stefaweb/Q17-Amplifier/Q17-Mini-3.0/Q17-Mini-L1-measure.jpg

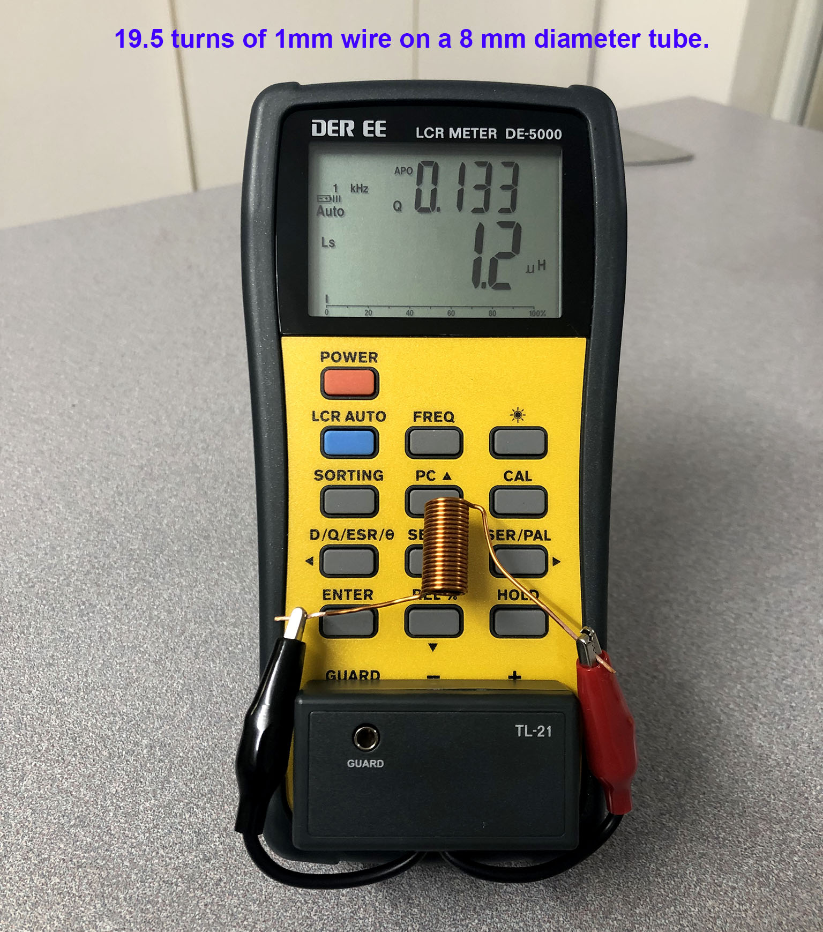
Q17-Mini-3.0/Q17-Mini-L1-measure.jpg
