stefaweb/Q17-Amplifier/Q17-Mini-PCB-1.0.8 2.jpg

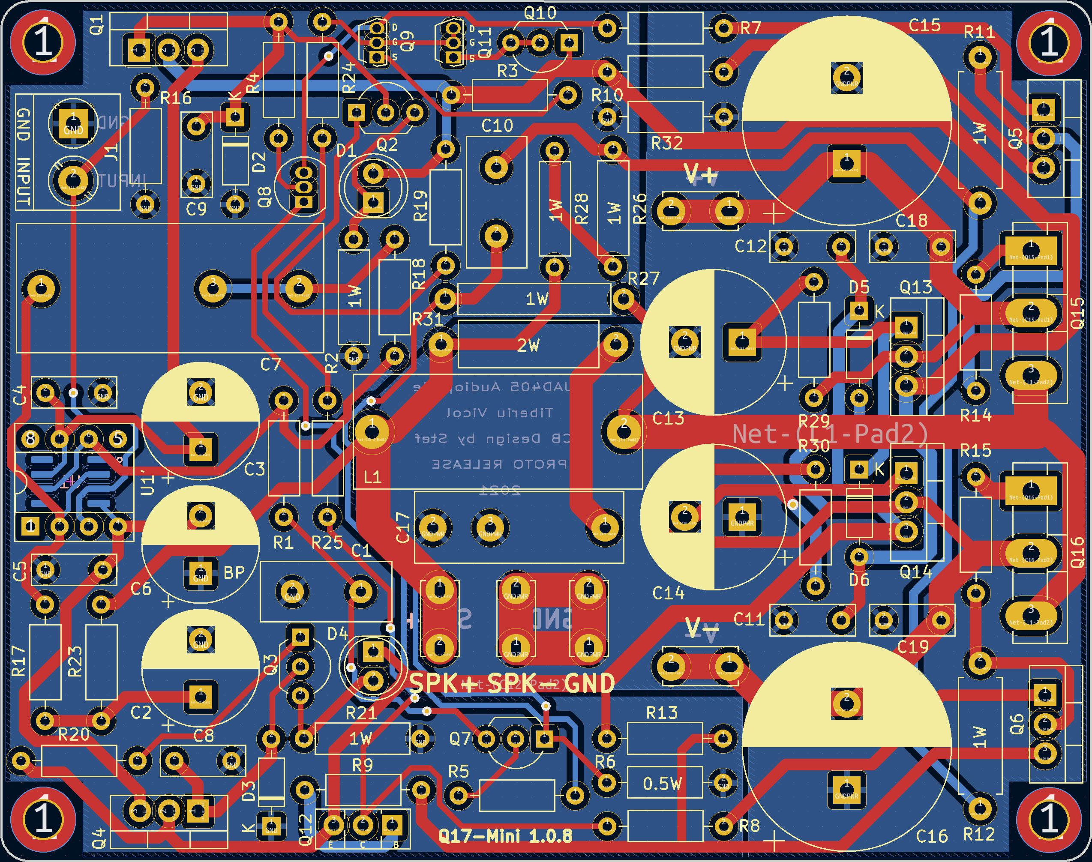
Q17-Mini-PCB-1.0.8 2.jpg
