stefaweb/Q17-Amplifier/NDC7003P KiCad/NDC7003P-Symbol.png

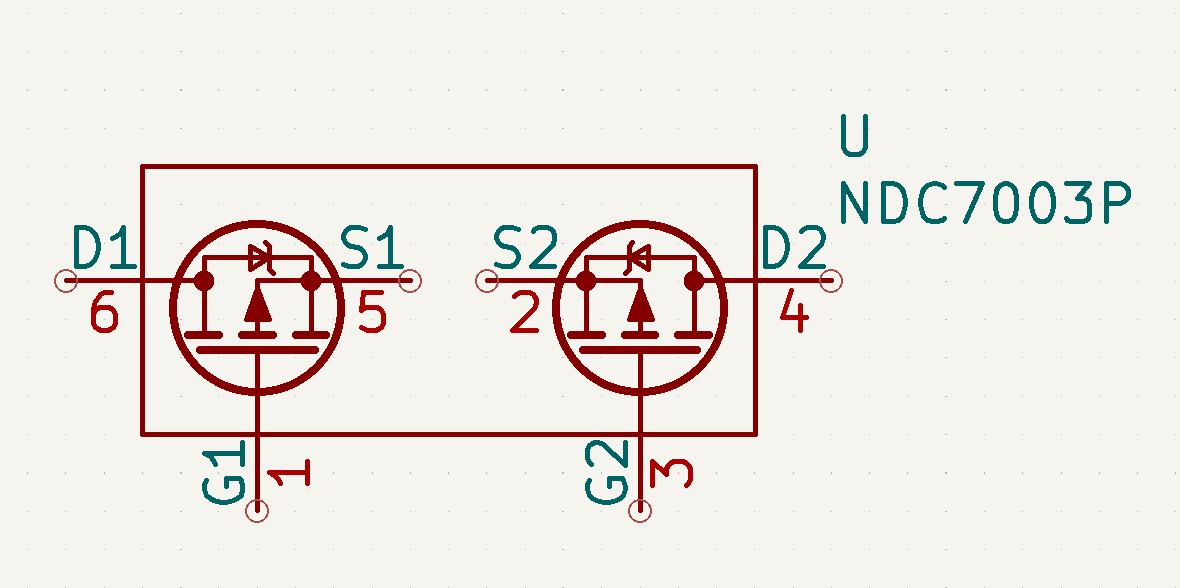
NDC7003P KiCad/NDC7003P-Symbol.png
