stefaweb/Q17-Amplifier/Q17-Mini-1.1.1/Q17-Mini-PCB.jpg

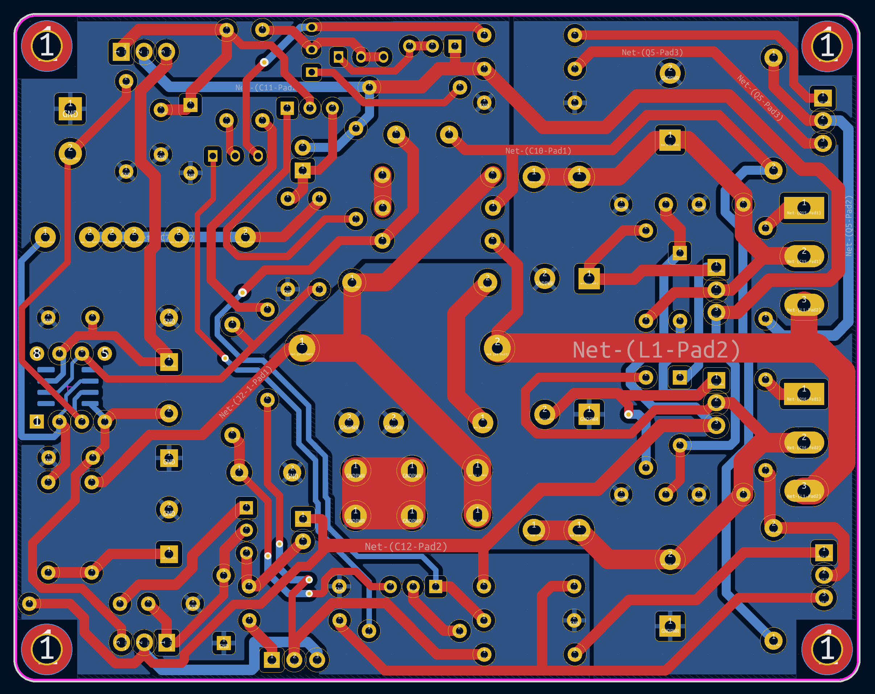
Q17-Mini-1.1.1/Q17-Mini-PCB.jpg
