stefaweb/Q17-Amplifier/Q17-Mini-3.0/Drilling diagram Q17-Mini v3.jpg

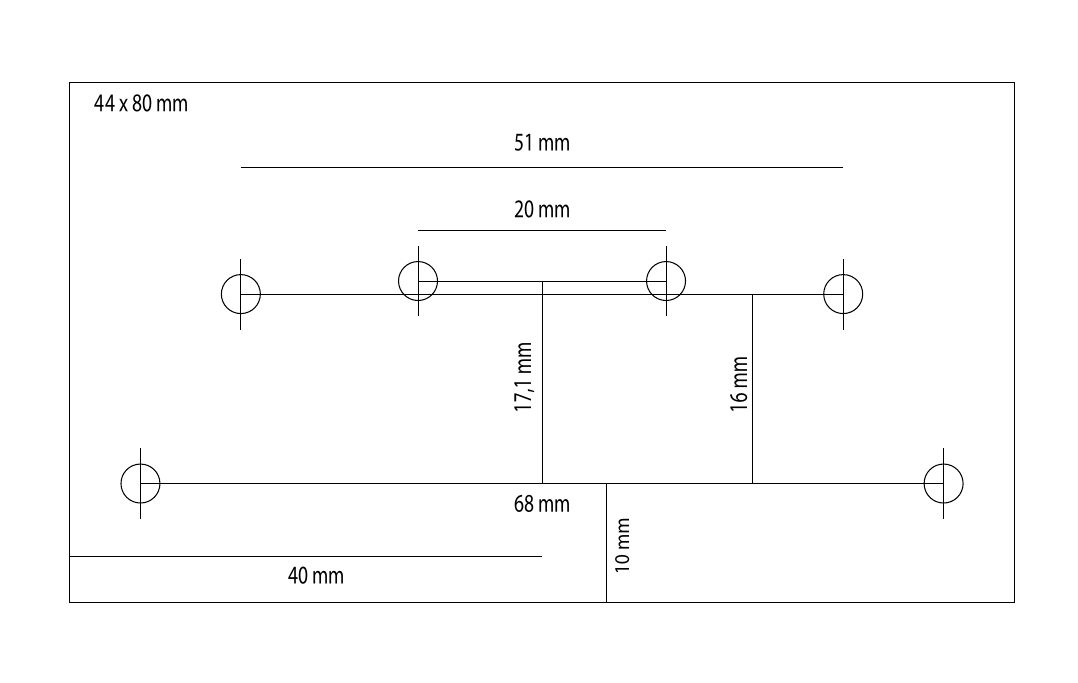
Q17-Mini-3.0/Drilling diagram Q17-Mini v3.jpg
