stefaweb/Q17-Amplifier/Q17-Mini-3.0/Measures Q17-Mini 3.0/Q17-Mini-3.0-spectrum_OPA828.jpg

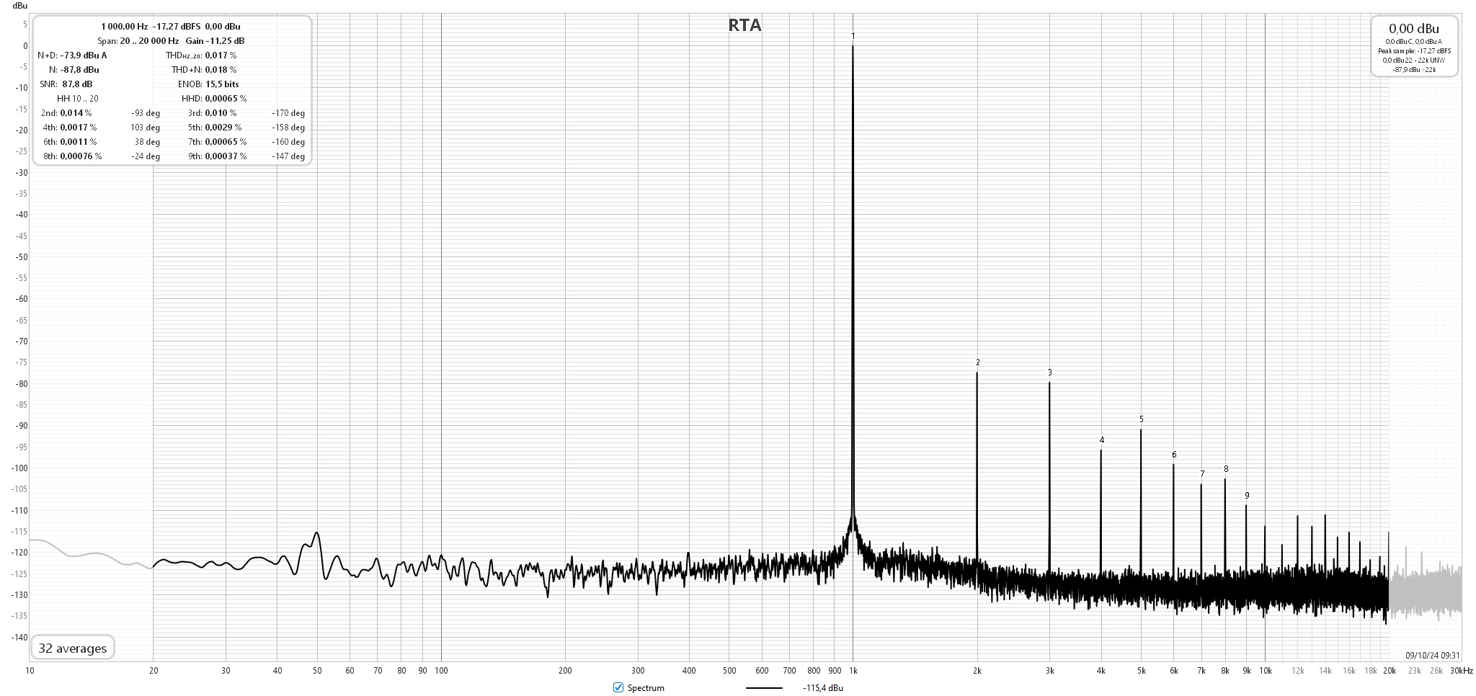
Q17-Mini-3.0/Measures Q17-Mini 3.0/Q17-Mini-3.0-spectrum_OPA828.jpg
