stefaweb/Q17-Amplifier/Q17-Mini-3.0/Q17-Mini-PCB-FRONT.jpg

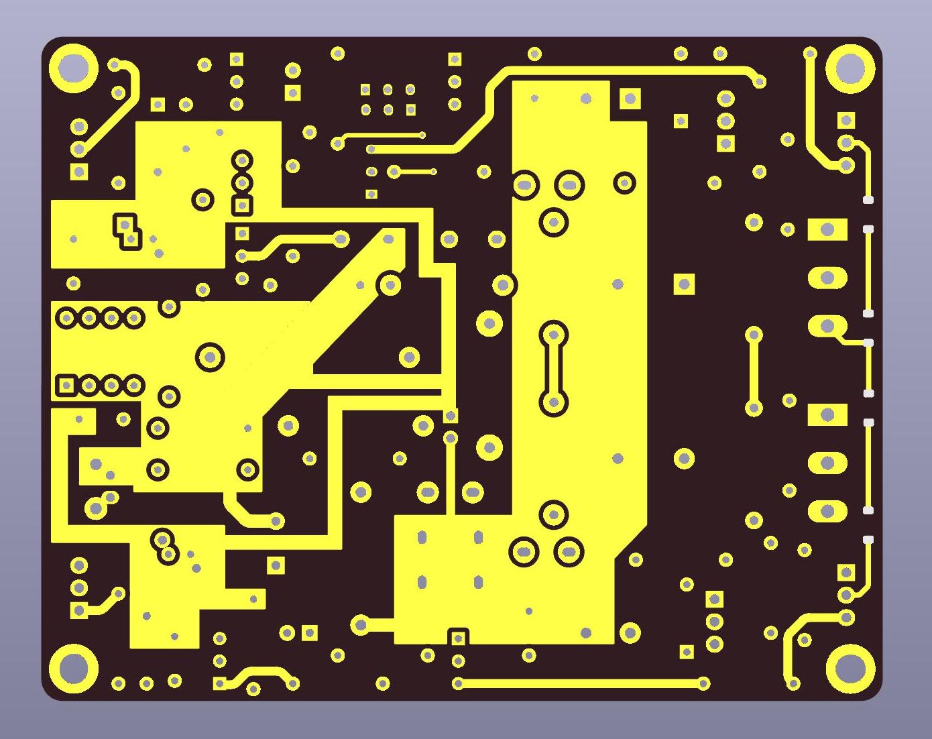
Q17-Mini-3.0/Q17-Mini-PCB-FRONT.jpg
