stefaweb/Q17-Amplifier/Q17-PCB-Coil 1.1/pcb_coil_1.2uH.jpg

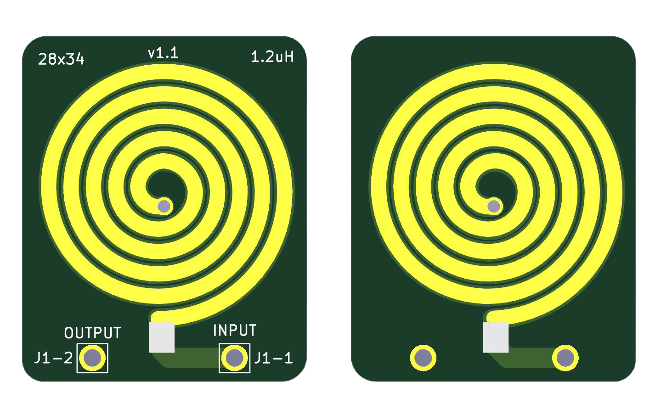
Q17-PCB-Coil 1.1/pcb_coil_1.2uH.jpg
