stefaweb/Q17-Amplifier/Q17-TURBO 1.0/Q17-TURBO-3D.jpg

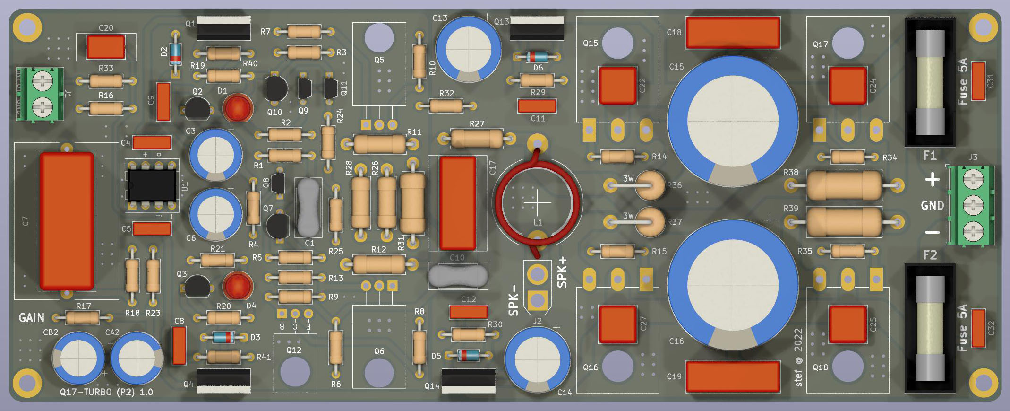
Q17-TURBO 1.0/Q17-TURBO-3D.jpg
