stefaweb/Q17-Amplifier/Q17-TURBO 1.0/Q17-TURBO-COIL-1.2uH/Wire_1.5mm2.jpeg

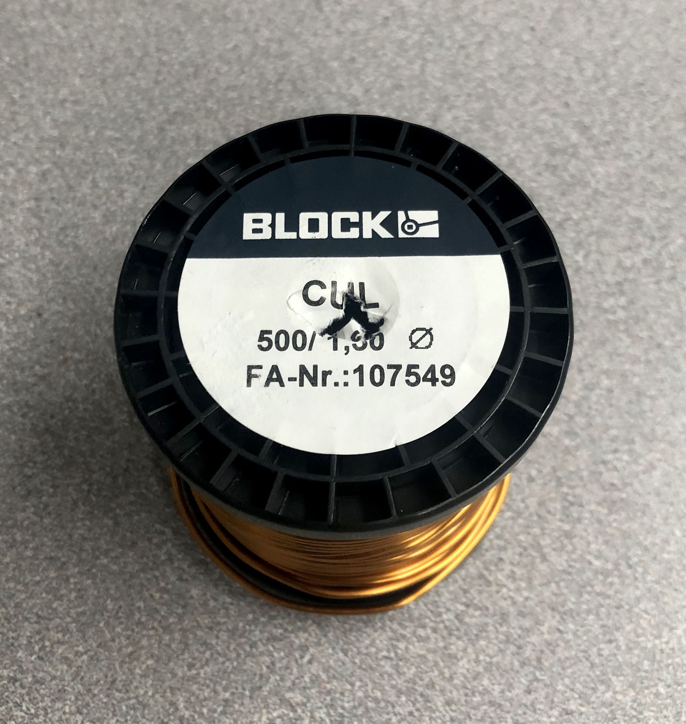
Q17-TURBO 1.0/Q17-TURBO-COIL-1.2uH/Wire_1.5mm2.jpeg
