stefaweb/Q17-Amplifier/Q17-TURBO-2.0/Mounting Plate-Q17-Turbo-216x80-1.0.png

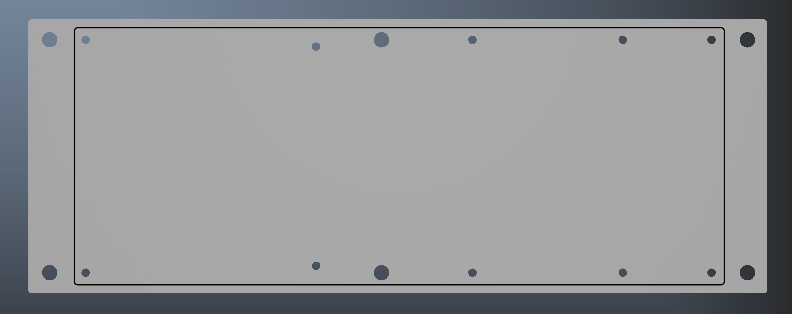
Q17-TURBO-2.0/Mounting Plate-Q17-Turbo-216x80-1.0.png
