stefaweb/Q17-Amplifier/Q17-TURBO-2.0/Q17-Turbo v2 Damping Factor.jpg

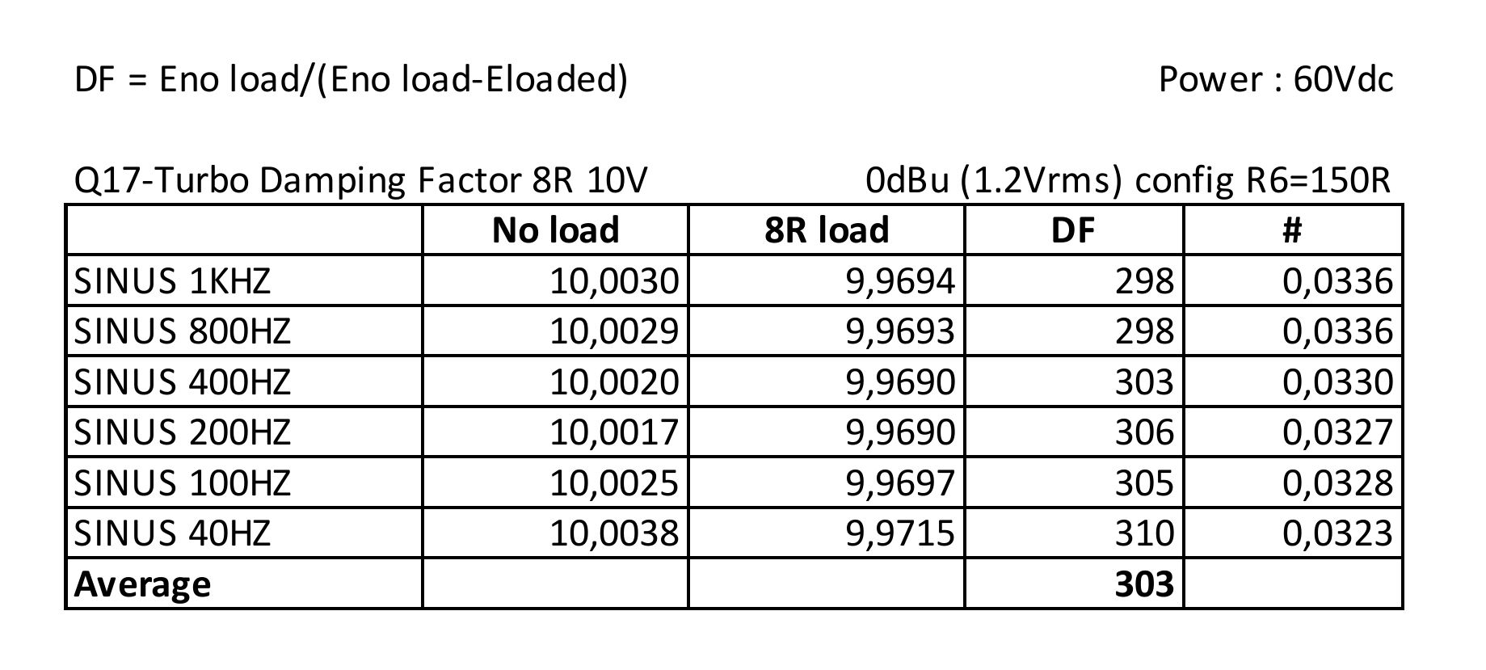
Q17-TURBO-2.0/Q17-Turbo v2 Damping Factor.jpg
