stefaweb/Q17-Amplifier/Q17-TURBO-2.0/Q17-TURBO-3D-BACK.jpg

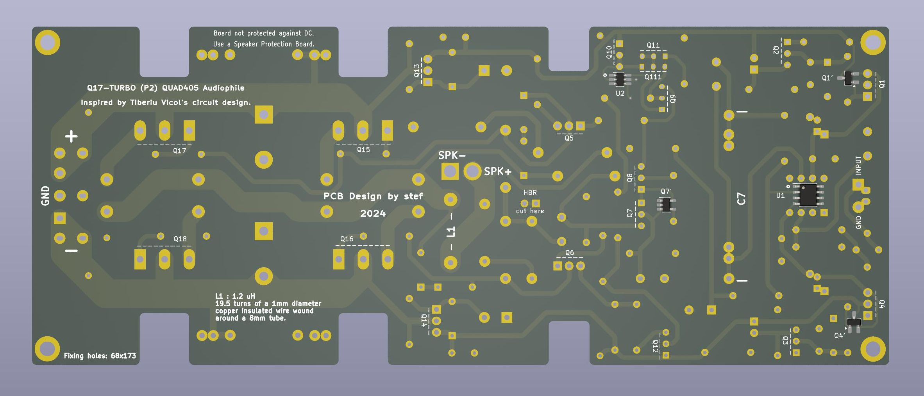
Q17-TURBO-2.0/Q17-TURBO-3D-BACK.jpg
