stefaweb/Q17-Amplifier/Q17-TURBO-2.0/Q17-TURBO-3D-VIEW.jpg

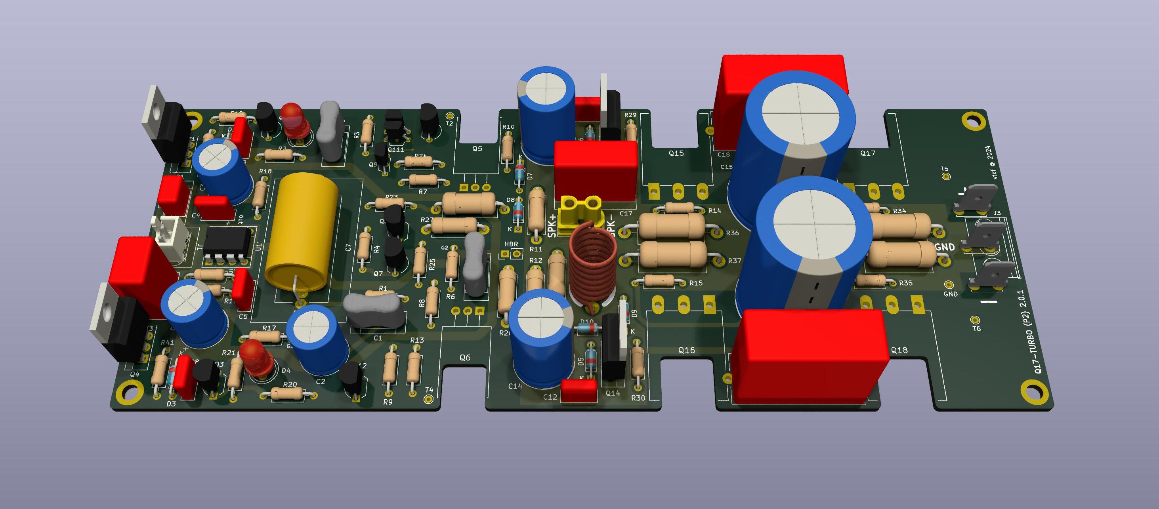
Q17-TURBO-2.0/Q17-TURBO-3D-VIEW.jpg
