stefaweb/Q17-Amplifier/Q17-Mini-3.0/Measures Q17-Mini 3.0/Q17-Mini-3.0_distorsion_1W_configA4.jpg

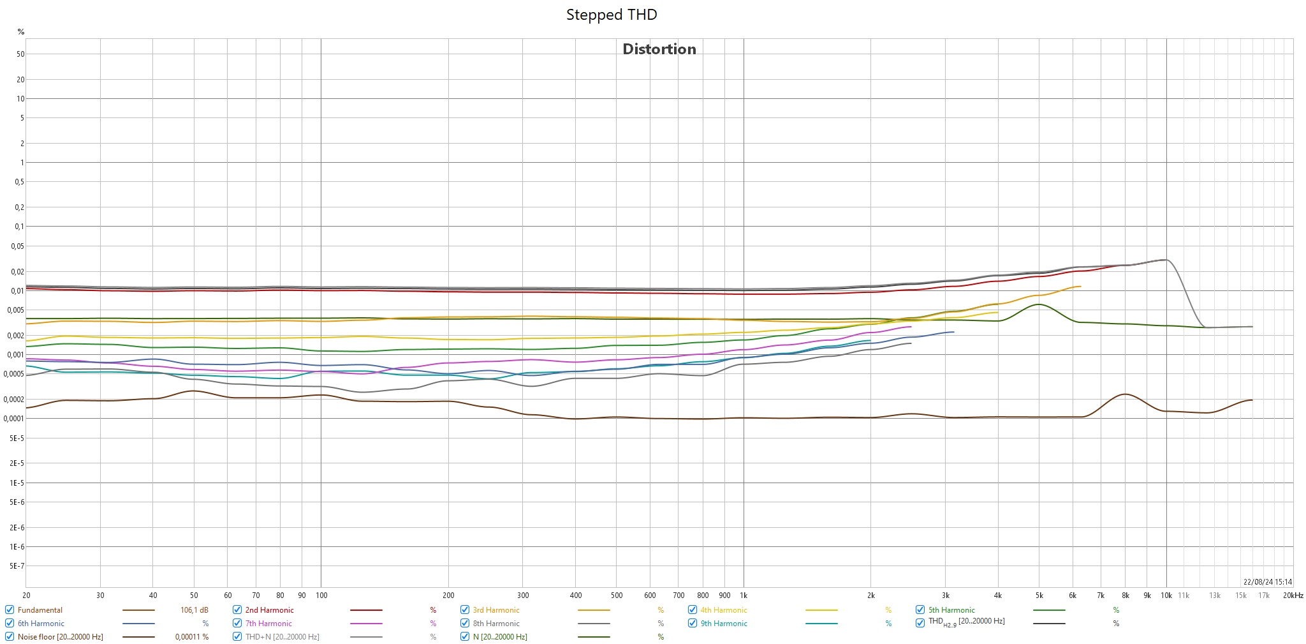
Q17-Mini-3.0/Measures Q17-Mini 3.0/Q17-Mini-3.0_distorsion_1W_configA4.jpg
