stefaweb/Q17-Amplifier/Q17-Mini-3.0/Measures Q17-Mini 3.0/SQUARE_1KHz_1W.jpg

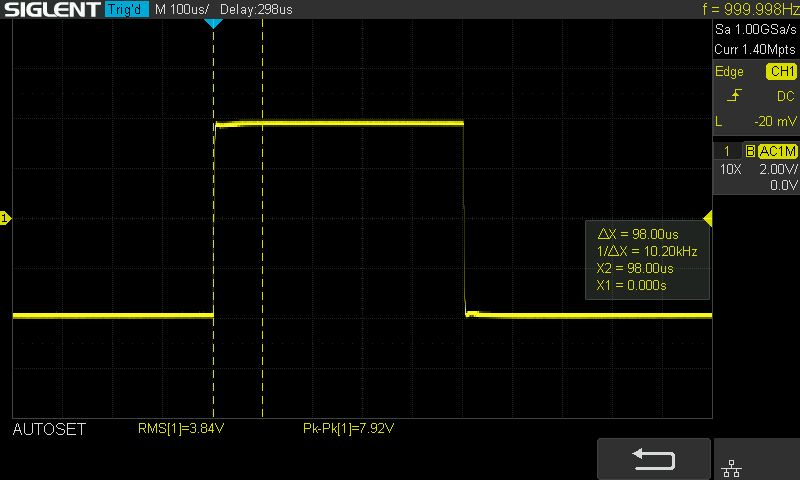
Q17-Mini-3.0/Measures Q17-Mini 3.0/SQUARE_1KHz_1W.jpg
