stefaweb/Q17-Amplifier/Q17-TURBO 1.0/Measures Q17-Turbo 1.0/Q17-Turbo-square-1Khz-50v-clip.jpg

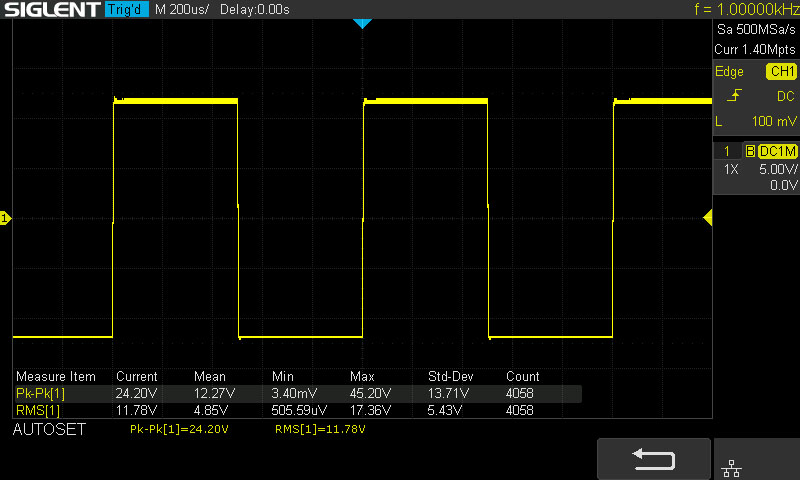
Q17-TURBO 1.0/Measures Q17-Turbo 1.0/Q17-Turbo-square-1Khz-50v-clip.jpg
