stefaweb/Q17-Amplifier/Q17-TURBO-2.0/Measures Q17-Turbo 2.0/SINUS_1KHz_1W.jpg

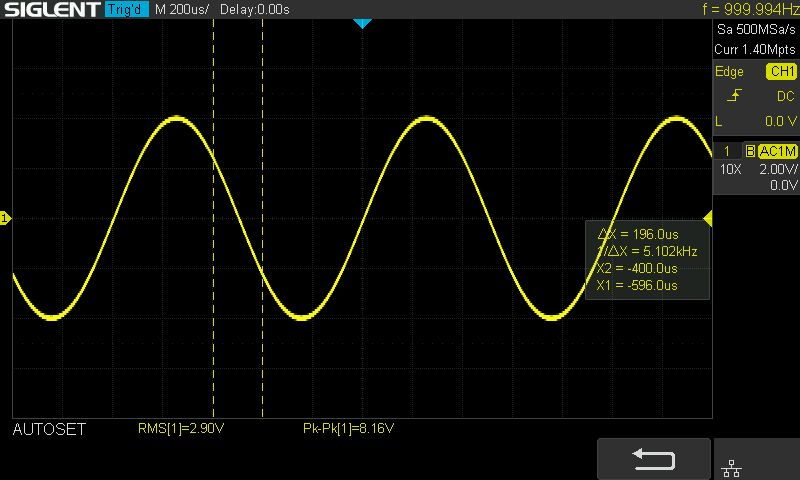
Q17-TURBO-2.0/Measures Q17-Turbo 2.0/SINUS_1KHz_1W.jpg
