stefaweb/Q17-Amplifier/KiCad source/Q17-95x75.kicad_sch

## KiCad design KiCad source/Q17-95x75.kicad_sch (2021-11-15)

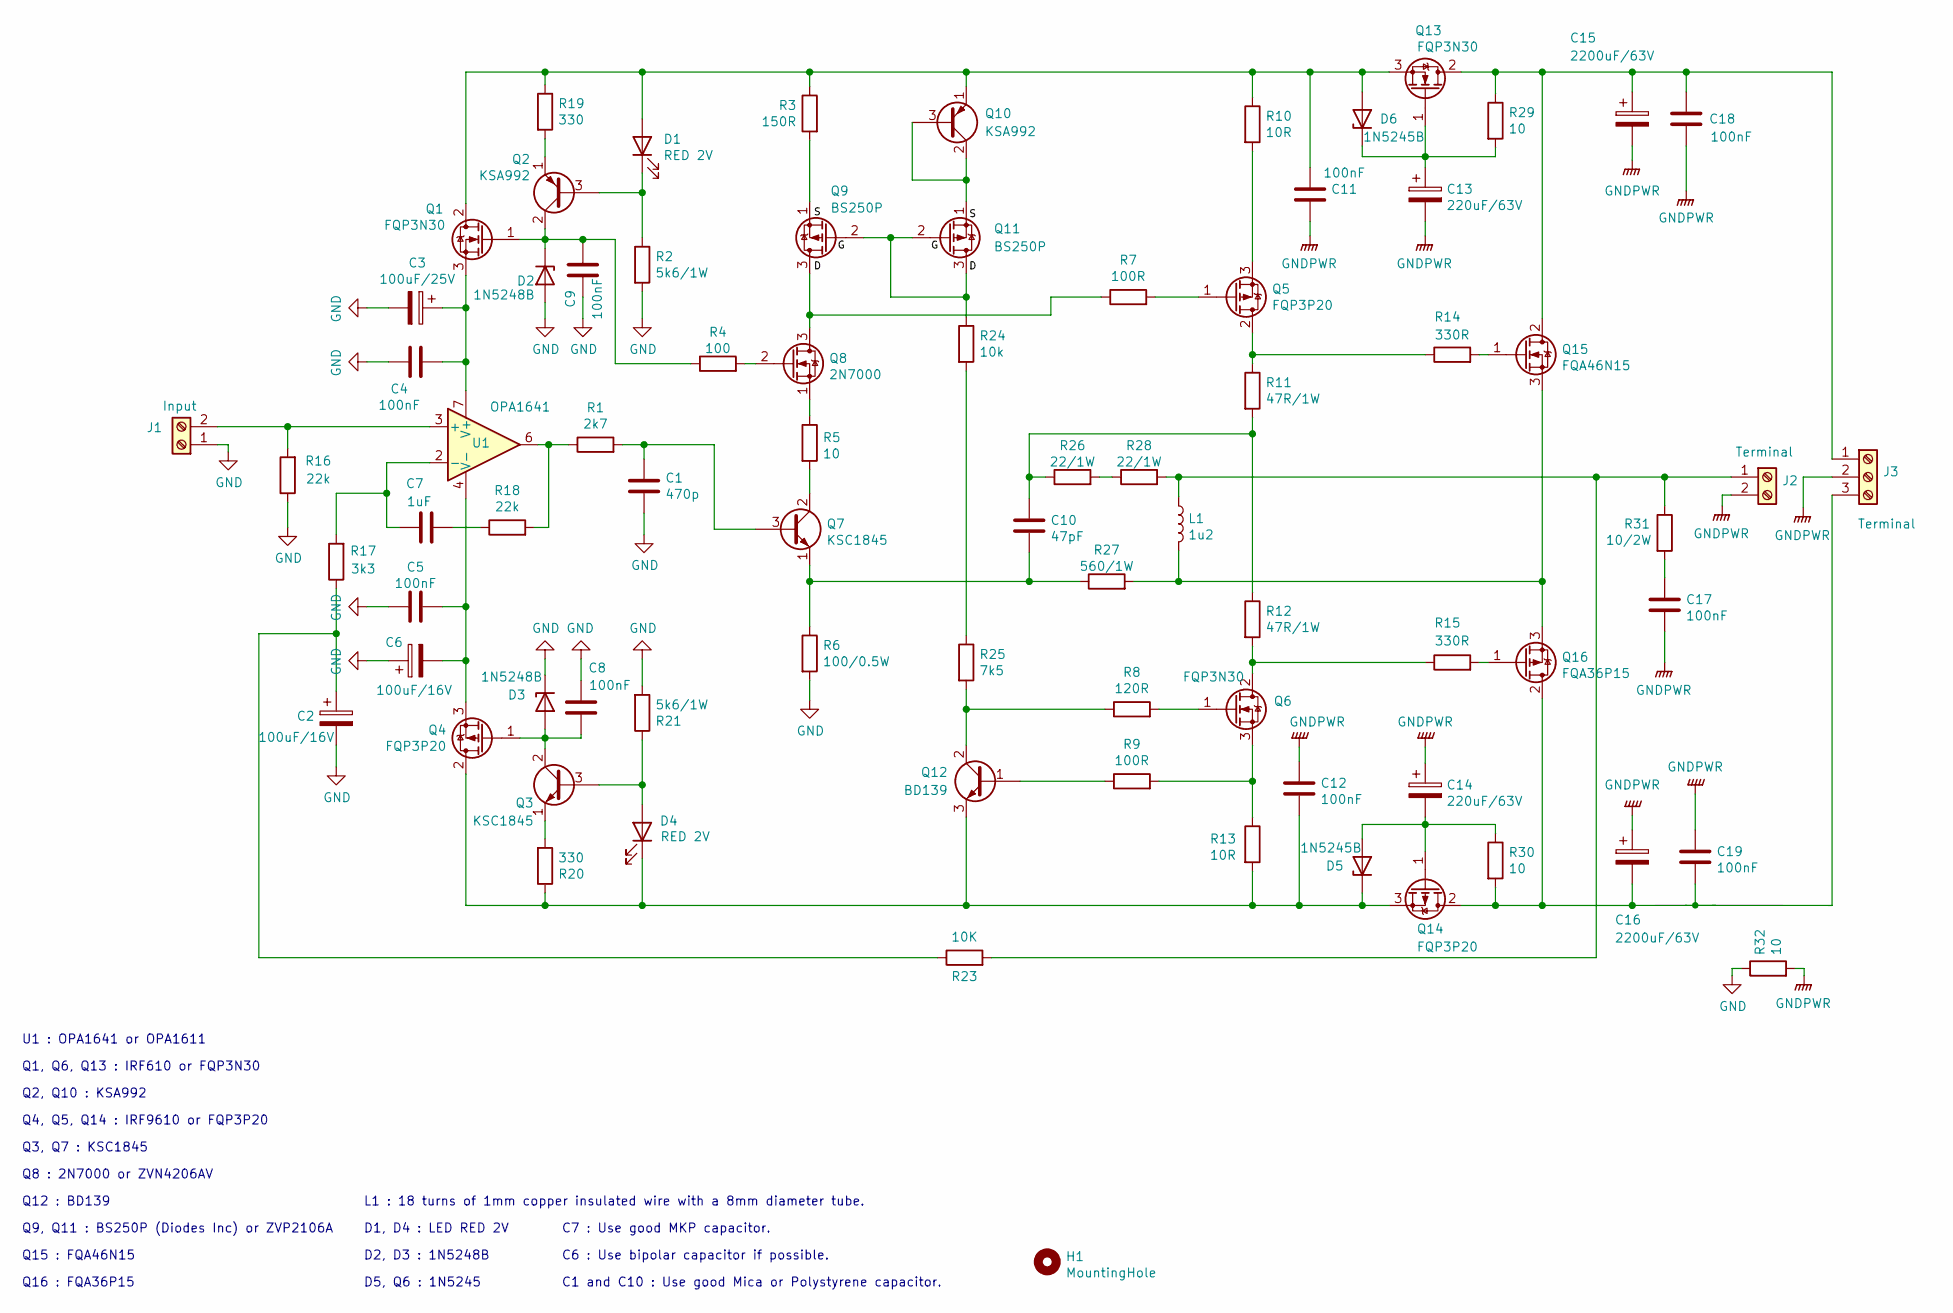
[picture p69: schematic Q17-95x75.kicad_sch]

Parts:
C1: 470p; C_Disc_D11.0mm_W5.0mm_P7.50mm
C2, C6: 100uF/16V; C_Radial_D10.0mm_H12.5mm_P5.00mm
C3: 100uF/25V; C_Radial_D10.0mm_H12.5mm_P5.00mm
C4, C5, C8, C9, C11, C12, C18, C19: 100nF; C_Disc_D7.5mm_W2.5mm_P5.00mm
C7: 1uF; CP_Axial_L26.5mm_D20.0mm_P33.00mm_Horizontal
C10: 47pF; C_Disc_D11.0mm_W5.0mm_P7.50mm
C13, C14: 220uF/63V; CP_Radial_D10.0mm_P5.00mm_P7.50mm
C15, C16: 2200uF/63V; CP_Radial_D18.0mm_P7.50mm
C17: 100nF; C_Rect_L18.0mm_W11.0mm_P15.00mm_FKS3_FKP3
D1, D4: RED 2V; LED_D5.0mm_Clear
D2, D3: 1N5248B; D_DO-35_SOD27_P7.62mm_Horizontal
D5, D6: 1N5245B; D_DO-35_SOD27_P7.62mm_Horizontal
H1: MountingHole; MountingHole_3.2mm_M3_Pad_Via
J1: Input; Stocko_MKS_1651-6-0-202_1x2_P2.50mm_Vertical
J2: Terminal; AMASS_XT30U-F_1x02_P5.0mm_Vertical
J3: Terminal; TerminalBlock_Altech_AK300-3_P5.00mm
L1: 1u2; L
Q1, Q6, Q13: FQP3N30; TO-220-3_Vertical
Q2, Q10: KSA992; TO-92
Q3, Q7: KSC1845; TO-92
Q4, Q5, Q14: FQP3P20; TO-220-3_Vertical
Q8: 2N7000; TO-92_Inline
Q9, Q11: BS250P; TO-92_Inline
Q12: BD139; TO-126-3_Vertical
Q15: FQA46N15; TO-3P-3_Horizontal_TabDown
Q16: FQA36P15; TO-3P-3_Horizontal_TabDown
R1: 2k7; R_Axial_DIN0207_L6.3mm_D2.5mm_P10.16mm_Horizontal
R2, R21: 5k6/1W; R_Axial_DIN0207_L6.3mm_D2.5mm_P10.16mm_Horizontal
R3: 150R; R_Axial_DIN0207_L6.3mm_D2.5mm_P10.16mm_Horizontal
R4: 100; R_Axial_DIN0207_L6.3mm_D2.5mm_P10.16mm_Horizontal
R5, R29, R30, R32: 10; R_Axial_DIN0207_L6.3mm_D2.5mm_P10.16mm_Horizontal
R6: 100/0.5W; R_Axial_DIN0207_L6.3mm_D2.5mm_P10.16mm_Horizontal
R7, R9: 100R; R_Axial_DIN0207_L6.3mm_D2.5mm_P10.16mm_Horizontal
R8: 120R; R_Axial_DIN0207_L6.3mm_D2.5mm_P10.16mm_Horizontal
R10, R13: 10R; R_Axial_DIN0207_L6.3mm_D2.5mm_P10.16mm_Horizontal
R11, R12: 47R/1W; R_Axial_DIN0411_L9.9mm_D3.6mm_P12.70mm_Horizontal
R14, R15: 330R; R_Axial_DIN0207_L6.3mm_D2.5mm_P10.16mm_Horizontal
R16, R18: 22k; R_Axial_DIN0207_L6.3mm_D2.5mm_P10.16mm_Horizontal
R17: 3k3; R_Axial_DIN0207_L6.3mm_D2.5mm_P10.16mm_Horizontal
R19, R20: 330; R_Axial_DIN0207_L6.3mm_D2.5mm_P10.16mm_Horizontal
R23: 10K; R_Axial_DIN0207_L6.3mm_D2.5mm_P10.16mm_Horizontal
R24: 10k; R_Axial_DIN0207_L6.3mm_D2.5mm_P10.16mm_Horizontal
R25: 7k5; R_Axial_DIN0207_L6.3mm_D2.5mm_P10.16mm_Horizontal
R26, R28: 22/1W; R_Axial_DIN0207_L6.3mm_D2.5mm_P10.16mm_Horizontal
R27: 560/1W; R_Axial_DIN0207_L6.3mm_D2.5mm_P10.16mm_Horizontal
R31: 10/2W; R_Axial_DIN0309_L9.0mm_D3.2mm_P12.70mm_Horizontal
U1: OPA1641; SOIC-8_3.9x4.9mm_P1.27mm

Connections:
GND: C1.2, C2.2, C3.2, C4.1, C5.1, C6.1, C8.1, C9.1, D2.2 (A), D3.1 (K), J1.1, R2.2, R6.2, R16.1, R21.2, R32.1
GNDPWR: C11.1, C12.1, C13.2, C14.1, C15.2, C16.1, C17.2, C18.1, C19.2, J2.2, J3.2, R32.2
unnamed: C1.1, Q7.3 (B), R1.2
unnamed: C2.1, R17.1, R23.1
unnamed: C3.1, C4.2, Q1.3 (S), U1.7 (V+)
unnamed: C5.2, C6.2, Q4.3 (S), U1.4 (V-)
unnamed: C7.1, R18.1
unnamed: C7.2, R17.2, U1.2 (-)
unnamed: C8.2, D3.2 (A), Q3.2 (C), Q4.1 (G)
unnamed: C9.2, D2.1 (K), Q1.1 (G), Q2.2 (C), R4.1
unnamed: C10.1, R11.2, R12.1, R26.1
unnamed: C10.2, Q7.1 (E), R6.1, R27.1
unnamed: C11.2, D1.2 (A), D6.2 (A), Q1.2 (D), Q10.1 (E), Q13.3 (S), R3.1, R10.1, R19.1
unnamed: C12.2, D4.1 (K), D5.1 (K), Q4.2 (D), Q12.3 (E), Q14.3 (S), R13.2, R20.1
unnamed: C13.1, D6.1 (K), Q13.1 (G), R29.2
unnamed: C14.2, D5.2 (A), Q14.1 (G), R30.1
unnamed: C15.1, C18.2, J3.1, Q13.2 (D), Q15.2 (D), R29.1
unnamed: C16.2, C19.1, J3.3, Q14.2 (D), Q16.2 (D), R30.2
unnamed: C17.1, R31.2
unnamed: D1.1 (K), Q2.3 (B), R2.1
unnamed: D4.2 (A), Q3.3 (B), R21.1
unnamed: J1.2, R16.2, U1.3 (+)
unnamed: J2.1, L1.1, R23.2, R28.2, R31.1
unnamed: L1.2, Q15.3 (S), Q16.3 (S), R27.2
unnamed: Q2.1 (E), R19.2
unnamed: Q3.1 (E), R20.2
unnamed: Q5.1 (G), R7.2
unnamed: Q5.2 (D), R11.1, R14.1
unnamed: Q5.3 (S), R10.2
unnamed: Q6.1 (G), R8.2
unnamed: Q6.2 (D), R12.2, R15.1
unnamed: Q6.3 (S), R9.2, R13.1
unnamed: Q7.2 (C), R5.2
unnamed: Q8.1 (S), R5.1
unnamed: Q8.2 (G), R4.2
unnamed: Q8.3 (D), Q9.3 (D), R7.1
unnamed: Q9.1 (S), R3.2
unnamed: Q10.2 (C), Q10.3 (B), Q11.1 (S)
unnamed: Q9.2 (G), Q11.2 (G), Q11.3 (D), R24.1
unnamed: Q12.1 (B), R9.1
unnamed: Q12.2 (C), R8.1, R25.2
unnamed: Q15.1 (G), R14.2
unnamed: Q16.1 (G), R15.2
unnamed: R1.1, R18.2, U1.6
unnamed: R24.2, R25.1
unnamed: R26.2, R28.1

Notes on the sheet:
C1 and C10 : Use good Mica or Polystyrene capacitor.
Q12 : BD139
C7 : Use good MKP capacitor.
D2, D3 : 1N5248B
Q2, Q10 : KSA992
D1, D4 : LED RED 2V
Q3, Q7 : KSC1845
C6 : Use bipolar capacitor if possible.
Q4, Q5, Q14 : IRF9610 or FQP3P20
Q15 : FQA46N15
Q1, Q6, Q13 : IRF610 or FQP3N30
Q9, Q11 : BS250P (Diodes Inc) or ZVP2106A
U1 : OPA1641 or OPA1611
D5, Q6 : 1N5245
L1 : 18 turns of 1mm copper insulated wire with a 8mm diameter tube.
Q8 : 2N7000 or ZVN4206AV
Q16 : FQA36P15
